grantek/minisynth32/3d_models/shim-0.8mm.stl

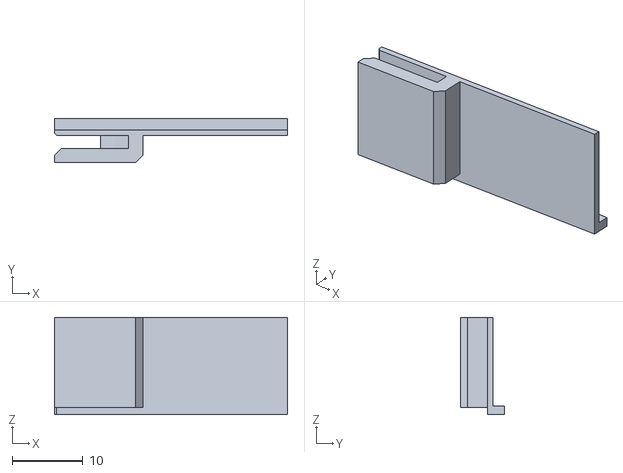
[picture p17: CAD file, 2021-10-08]
3d_models/shim-0.8mm.stl
33.0 x 6.20 x 13.8
