grantek/minisynth32/3d_models/rectbutton.FCStd

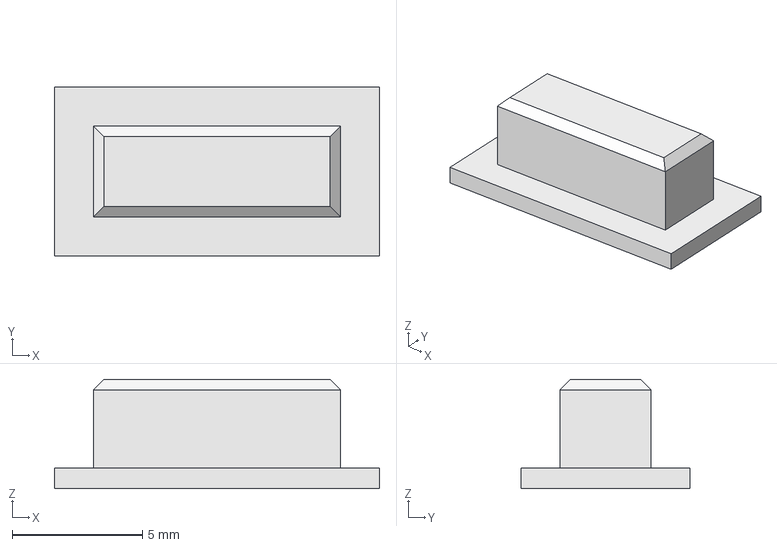
[picture p18: CAD file, 2021-10-08]
3d_models/rectbutton.FCStd
12.5 x 6.50 x 4.20 mm
