grantek/minisynth32/3d_models/base-din.stl

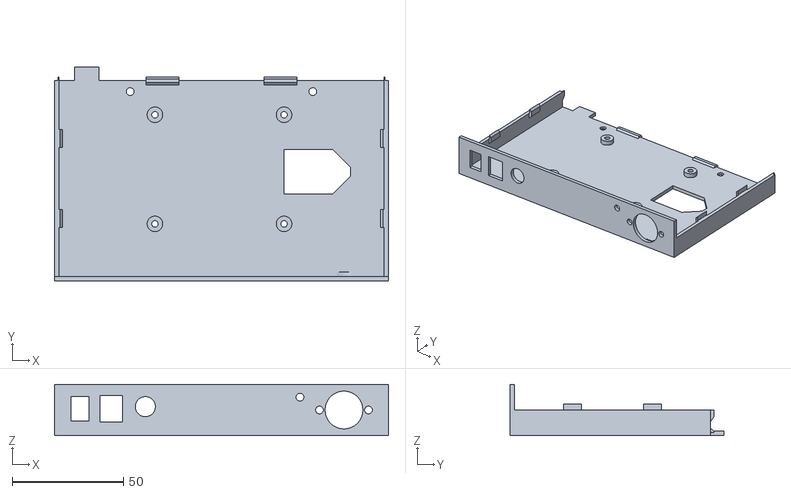
[picture p19: CAD file, 2021-10-08]
3d_models/base-din.stl
150.0 x 96.0 x 23.0
