grantek/minisynth32/3d_models/rebackplate.FCStd

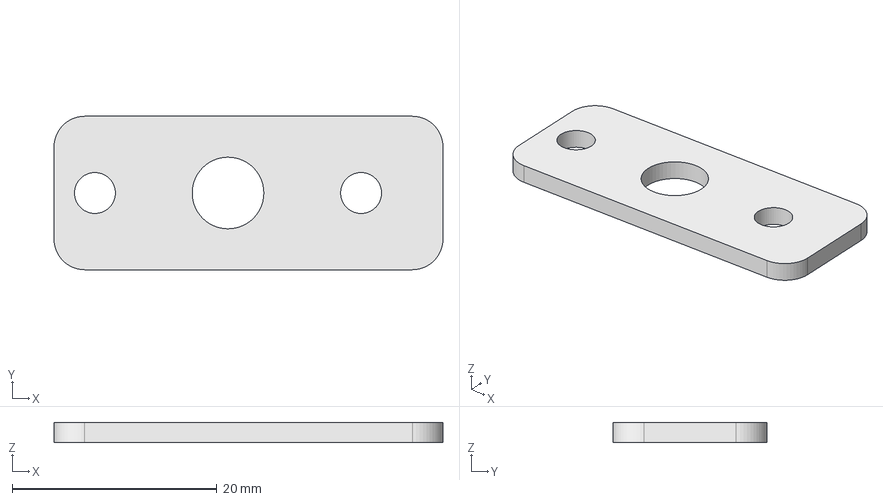
[picture p20: CAD file, 2021-08-01]
3d_models/rebackplate.FCStd
38.0 x 15.0 x 2.00 mm
