grantek/minisynth32/3d_models/knob-3.1mm.FCStd

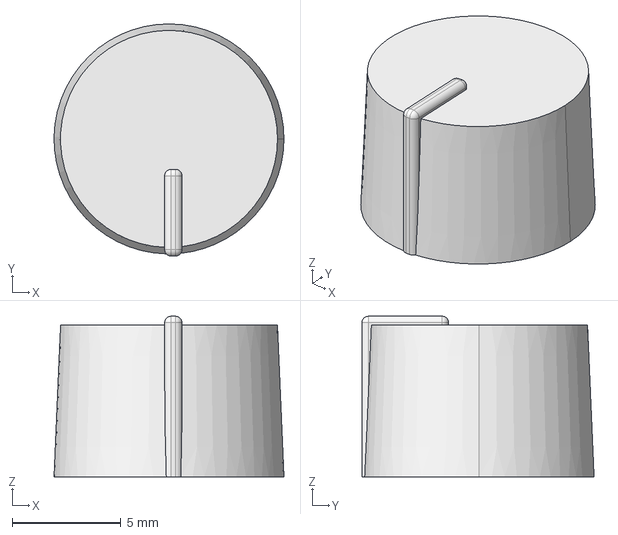
[picture p21: CAD file, 2021-05-17]
3d_models/knob-3.1mm.FCStd
10.6 x 10.7 x 7.40 mm
